bjohnson66/wayfindx/docs/Doxygen/latex/utilities_8h.tex

\doxysection{G\+:/\+Project\+\_\+\+Files/\+Way\+Find\+X/wfx\+\_\+sw/wfx\+\_\+sw/ut/utilities.h File Reference}
\hypertarget{utilities_8h}{}\label{utilities_8h}\index{G:/Project\_Files/WayFindX/wfx\_sw/wfx\_sw/ut/utilities.h@{G:/Project\_Files/WayFindX/wfx\_sw/wfx\_sw/ut/utilities.h}}

Header file containing common utility functions and definitions.  

{\ttfamily \#include "{}ut\+\_\+types.\+h"{}}\newline
{\ttfamily \#include "{}../nf/nf\+\_\+types.\+h"{}}\newline
\doxysubsubsection*{Macros}
\begin{DoxyCompactItemize}
\item 
\#define \mbox{\hyperlink{utilities_8h_a700f88377bf36711b711f69b06c52f5d}{NOP}}~asm("{}nop"{});
\item 
\#define \mbox{\hyperlink{utilities_8h_a3c5465ec3dcb8f48d76b9961625cfb26}{STAT\+\_\+\+MODE}}~1
\item 
\#define \mbox{\hyperlink{utilities_8h_a2c6fab7bc1954d43f20ddcf3241d374f}{NAV\+\_\+\+MODE}}~0
\item 
\#define \mbox{\hyperlink{utilities_8h_a15ce356b42b1e66c0e5287551fbcd371}{NUM\+\_\+\+OPERATIONS}}~3
\item 
\#define \mbox{\hyperlink{utilities_8h_a44262718e6ca1ed8813bac3fe8c817c8}{SAVE\+\_\+\+OP}}~0
\item 
\#define \mbox{\hyperlink{utilities_8h_a8d067386e33f9d834262ff6bef0b4e0e}{CLEAR\+\_\+\+OP}}~1
\item 
\#define \mbox{\hyperlink{utilities_8h_a6dda44ab465064ec1dd8254e31b32d3d}{RESET\+\_\+\+OP}}~2
\item 
\#define \mbox{\hyperlink{utilities_8h_a30682ad456c44dd32e1da9094a40d97f}{MAX\+\_\+\+MEM\+\_\+\+INDEX}}~10
\item 
\#define \mbox{\hyperlink{utilities_8h_ac859a452892e212dd0cdbedf6f17318d}{SAVE\+\_\+\+STR}}~"{} SAVE"{}
\item 
\#define \mbox{\hyperlink{utilities_8h_a315549aca62f71abb3dfe8fd1770039a}{CLEAR\+\_\+\+STR}}~"{}CLEAR"{}
\item 
\#define \mbox{\hyperlink{utilities_8h_a3d3c836976b73a779f04cec0548df7c8}{RESET\+\_\+\+STR}}~"{}RESET"{}
\item 
\#define \mbox{\hyperlink{utilities_8h_a45add6b39f5b0c0137de978b90e26b5d}{NUM\+\_\+\+BUTTONS}}~4
\item 
\#define \mbox{\hyperlink{utilities_8h_a665ea61ca014eadbe2547eaf1b937fc3}{MODE\+\_\+\+SELECT\+\_\+\+BTN}}~PINC0
\item 
\#define \mbox{\hyperlink{utilities_8h_ae26947bd73f06a8fbe1720b9f1d0b4b0}{MEM\+\_\+\+SELECT\+\_\+\+BTN}}~PINC1
\item 
\#define \mbox{\hyperlink{utilities_8h_a1c07d5e59549b9f820a7f914cc9268e3}{OP\+\_\+\+SELECT\+\_\+\+BTN}}~PINC2
\item 
\#define \mbox{\hyperlink{utilities_8h_a8c37fc7873fc7e7e8f6c9a02f02e3a81}{ACTION\+\_\+\+BTN}}~PINC3
\item 
\#define \mbox{\hyperlink{utilities_8h_a6e14e133a57aa56366a16aa61f11453f}{ON\+\_\+\+TIME\+\_\+\+THRESHHOLD}}~(\mbox{\hyperlink{ut__types_8h_a1f1825b69244eb3ad2c7165ddc99c956}{uint16\+\_\+t}})100
\item 
\#define \mbox{\hyperlink{utilities_8h_a76b15c613ec428b45529947b62420051}{RESET\+\_\+\+TIME\+\_\+\+THRESHHOLD}}~(\mbox{\hyperlink{ut__types_8h_a1f1825b69244eb3ad2c7165ddc99c956}{uint16\+\_\+t}})30
\end{DoxyCompactItemize}
\doxysubsubsection*{Functions}
\begin{DoxyCompactItemize}
\item 
void \mbox{\hyperlink{utilities_8h_a435a2ff90939883d4bf4aa83f03cd2b4}{ut\+\_\+init}} ()
\begin{DoxyCompactList}\small\item\em Initializes the pins for buttons, loads from SD card, and initializes stored locations on startup. \end{DoxyCompactList}\item 
void \mbox{\hyperlink{utilities_8h_a88ffabf71aed5f9ff12e47960d74ad3a}{ut\+\_\+poll\+\_\+btns}} ()
\begin{DoxyCompactList}\small\item\em Checks status of each button sequentially. Action triggers on button release. Is to be called in background via interrupt. Post-\/polling action takes place in the following order\+: MODE\+\_\+\+SELECT\+\_\+\+BTN, MEM\+\_\+\+SELECT\+\_\+\+BTN, OP\+\_\+\+SELECT\+\_\+\+BTN. \end{DoxyCompactList}\end{DoxyCompactItemize}
\doxysubsubsection*{Variables}
\begin{DoxyCompactItemize}
\item 
\mbox{\hyperlink{ut__types_8h_a5338510a6d3a27844de9a766a4303d46}{boolean\+\_\+t}} \mbox{\hyperlink{utilities_8h_af78821a90ed17b6589cce61366448631}{ut\+\_\+mode}}
\item 
\mbox{\hyperlink{ut__types_8h_aba7bc1797add20fe3efdf37ced1182c5}{uint8\+\_\+t}} \mbox{\hyperlink{utilities_8h_a59ef0619f0fca92ab12dccac00503277}{ut\+\_\+operation}}
\item 
\mbox{\hyperlink{ut__types_8h_aba7bc1797add20fe3efdf37ced1182c5}{uint8\+\_\+t}} \mbox{\hyperlink{utilities_8h_aab6073f815c4c183a282ab1f8831e75a}{ut\+\_\+memory\+\_\+0idx}}
\item 
float \mbox{\hyperlink{utilities_8h_a41b8ed1a1c1e54b0bc8bd88cd0731187}{ut\+\_\+lat\+\_\+mem\+\_\+floats}} \mbox{[}\mbox{\hyperlink{utilities_8h_a30682ad456c44dd32e1da9094a40d97f}{MAX\+\_\+\+MEM\+\_\+\+INDEX}}\mbox{]}
\item 
float \mbox{\hyperlink{utilities_8h_a07f10ac2a8fd49e014aa87de20167da3}{ut\+\_\+long\+\_\+mem\+\_\+floats}} \mbox{[}\mbox{\hyperlink{utilities_8h_a30682ad456c44dd32e1da9094a40d97f}{MAX\+\_\+\+MEM\+\_\+\+INDEX}}\mbox{]}
\item 
char \mbox{\hyperlink{utilities_8h_ab7665b726dd42a9d5c9af514c3119768}{ut\+\_\+lat\+\_\+mem\+\_\+str}} \mbox{[}\mbox{\hyperlink{nf__types_8h_a7b3c9ba3ceea8208b4b82e11a41722e8}{LLA\+\_\+\+LAT\+\_\+\+BUFFER\+\_\+\+SIZE}}\mbox{]}
\item 
char \mbox{\hyperlink{utilities_8h_a22d6ca202177fcc59702e055ebb0e1e1}{ut\+\_\+long\+\_\+mem\+\_\+str}} \mbox{[}\mbox{\hyperlink{nf__types_8h_a548e32055b21b64df9a5c859e1be38d4}{LLA\+\_\+\+LONG\+\_\+\+BUFFER\+\_\+\+SIZE}}\mbox{]}
\end{DoxyCompactItemize}

\doxysubsection{Detailed Description}
Header file containing common utility functions and definitions. 

This file provides declarations for common utility functions and definitions that can be used throughout the project. \begin{DoxyVersion}{Version}
1.\+0 
\end{DoxyVersion}
\begin{DoxyCopyright}{Copyright}
(C) 2024 Bradley Johnson and Abele Atresso 
\end{DoxyCopyright}

Definition in file \mbox{\hyperlink{utilities_8h_source}{utilities.\+h}}.

\doxysubsection{Macro Definition Documentation}
\Hypertarget{utilities_8h_a8c37fc7873fc7e7e8f6c9a02f02e3a81}\label{utilities_8h_a8c37fc7873fc7e7e8f6c9a02f02e3a81} 
\index{utilities.h@{utilities.h}!ACTION\_BTN@{ACTION\_BTN}}
\index{ACTION\_BTN@{ACTION\_BTN}!utilities.h@{utilities.h}}
\doxysubsubsection{\texorpdfstring{ACTION\_BTN}{ACTION\_BTN}}
{\footnotesize\ttfamily \#define ACTION\+\_\+\+BTN~PINC3}

Action button pin. 

Definition at line \mbox{\hyperlink{utilities_8h_source_l00036}{36}} of file \mbox{\hyperlink{utilities_8h_source}{utilities.\+h}}.

\Hypertarget{utilities_8h_a8d067386e33f9d834262ff6bef0b4e0e}\label{utilities_8h_a8d067386e33f9d834262ff6bef0b4e0e} 
\index{utilities.h@{utilities.h}!CLEAR\_OP@{CLEAR\_OP}}
\index{CLEAR\_OP@{CLEAR\_OP}!utilities.h@{utilities.h}}
\doxysubsubsection{\texorpdfstring{CLEAR\_OP}{CLEAR\_OP}}
{\footnotesize\ttfamily \#define CLEAR\+\_\+\+OP~1}

Clear operation index. 

Definition at line \mbox{\hyperlink{utilities_8h_source_l00024}{24}} of file \mbox{\hyperlink{utilities_8h_source}{utilities.\+h}}.

\Hypertarget{utilities_8h_a315549aca62f71abb3dfe8fd1770039a}\label{utilities_8h_a315549aca62f71abb3dfe8fd1770039a} 
\index{utilities.h@{utilities.h}!CLEAR\_STR@{CLEAR\_STR}}
\index{CLEAR\_STR@{CLEAR\_STR}!utilities.h@{utilities.h}}
\doxysubsubsection{\texorpdfstring{CLEAR\_STR}{CLEAR\_STR}}
{\footnotesize\ttfamily \#define CLEAR\+\_\+\+STR~"{}CLEAR"{}}

Clear operation string. 

Definition at line \mbox{\hyperlink{utilities_8h_source_l00029}{29}} of file \mbox{\hyperlink{utilities_8h_source}{utilities.\+h}}.

\Hypertarget{utilities_8h_a30682ad456c44dd32e1da9094a40d97f}\label{utilities_8h_a30682ad456c44dd32e1da9094a40d97f} 
\index{utilities.h@{utilities.h}!MAX\_MEM\_INDEX@{MAX\_MEM\_INDEX}}
\index{MAX\_MEM\_INDEX@{MAX\_MEM\_INDEX}!utilities.h@{utilities.h}}
\doxysubsubsection{\texorpdfstring{MAX\_MEM\_INDEX}{MAX\_MEM\_INDEX}}
{\footnotesize\ttfamily \#define MAX\+\_\+\+MEM\+\_\+\+INDEX~10}

Maximum memory index. 

Definition at line \mbox{\hyperlink{utilities_8h_source_l00027}{27}} of file \mbox{\hyperlink{utilities_8h_source}{utilities.\+h}}.

\Hypertarget{utilities_8h_ae26947bd73f06a8fbe1720b9f1d0b4b0}\label{utilities_8h_ae26947bd73f06a8fbe1720b9f1d0b4b0} 
\index{utilities.h@{utilities.h}!MEM\_SELECT\_BTN@{MEM\_SELECT\_BTN}}
\index{MEM\_SELECT\_BTN@{MEM\_SELECT\_BTN}!utilities.h@{utilities.h}}
\doxysubsubsection{\texorpdfstring{MEM\_SELECT\_BTN}{MEM\_SELECT\_BTN}}
{\footnotesize\ttfamily \#define MEM\+\_\+\+SELECT\+\_\+\+BTN~PINC1}

Memory select button pin. 

Definition at line \mbox{\hyperlink{utilities_8h_source_l00034}{34}} of file \mbox{\hyperlink{utilities_8h_source}{utilities.\+h}}.

\Hypertarget{utilities_8h_a665ea61ca014eadbe2547eaf1b937fc3}\label{utilities_8h_a665ea61ca014eadbe2547eaf1b937fc3} 
\index{utilities.h@{utilities.h}!MODE\_SELECT\_BTN@{MODE\_SELECT\_BTN}}
\index{MODE\_SELECT\_BTN@{MODE\_SELECT\_BTN}!utilities.h@{utilities.h}}
\doxysubsubsection{\texorpdfstring{MODE\_SELECT\_BTN}{MODE\_SELECT\_BTN}}
{\footnotesize\ttfamily \#define MODE\+\_\+\+SELECT\+\_\+\+BTN~PINC0}

Mode select button pin. 

Definition at line \mbox{\hyperlink{utilities_8h_source_l00033}{33}} of file \mbox{\hyperlink{utilities_8h_source}{utilities.\+h}}.

\Hypertarget{utilities_8h_a2c6fab7bc1954d43f20ddcf3241d374f}\label{utilities_8h_a2c6fab7bc1954d43f20ddcf3241d374f} 
\index{utilities.h@{utilities.h}!NAV\_MODE@{NAV\_MODE}}
\index{NAV\_MODE@{NAV\_MODE}!utilities.h@{utilities.h}}
\doxysubsubsection{\texorpdfstring{NAV\_MODE}{NAV\_MODE}}
{\footnotesize\ttfamily \#define NAV\+\_\+\+MODE~0}

Mode indicating navigation. 

Definition at line \mbox{\hyperlink{utilities_8h_source_l00020}{20}} of file \mbox{\hyperlink{utilities_8h_source}{utilities.\+h}}.

\Hypertarget{utilities_8h_a700f88377bf36711b711f69b06c52f5d}\label{utilities_8h_a700f88377bf36711b711f69b06c52f5d} 
\index{utilities.h@{utilities.h}!NOP@{NOP}}
\index{NOP@{NOP}!utilities.h@{utilities.h}}
\doxysubsubsection{\texorpdfstring{NOP}{NOP}}
{\footnotesize\ttfamily \#define NOP~asm("{}nop"{});}

No operation macro. 

Definition at line \mbox{\hyperlink{utilities_8h_source_l00017}{17}} of file \mbox{\hyperlink{utilities_8h_source}{utilities.\+h}}.

\Hypertarget{utilities_8h_a45add6b39f5b0c0137de978b90e26b5d}\label{utilities_8h_a45add6b39f5b0c0137de978b90e26b5d} 
\index{utilities.h@{utilities.h}!NUM\_BUTTONS@{NUM\_BUTTONS}}
\index{NUM\_BUTTONS@{NUM\_BUTTONS}!utilities.h@{utilities.h}}
\doxysubsubsection{\texorpdfstring{NUM\_BUTTONS}{NUM\_BUTTONS}}
{\footnotesize\ttfamily \#define NUM\+\_\+\+BUTTONS~4}

Number of buttons. 

Definition at line \mbox{\hyperlink{utilities_8h_source_l00032}{32}} of file \mbox{\hyperlink{utilities_8h_source}{utilities.\+h}}.

\Hypertarget{utilities_8h_a15ce356b42b1e66c0e5287551fbcd371}\label{utilities_8h_a15ce356b42b1e66c0e5287551fbcd371} 
\index{utilities.h@{utilities.h}!NUM\_OPERATIONS@{NUM\_OPERATIONS}}
\index{NUM\_OPERATIONS@{NUM\_OPERATIONS}!utilities.h@{utilities.h}}
\doxysubsubsection{\texorpdfstring{NUM\_OPERATIONS}{NUM\_OPERATIONS}}
{\footnotesize\ttfamily \#define NUM\+\_\+\+OPERATIONS~3}

Number of available operations. 

Definition at line \mbox{\hyperlink{utilities_8h_source_l00022}{22}} of file \mbox{\hyperlink{utilities_8h_source}{utilities.\+h}}.

\Hypertarget{utilities_8h_a6e14e133a57aa56366a16aa61f11453f}\label{utilities_8h_a6e14e133a57aa56366a16aa61f11453f} 
\index{utilities.h@{utilities.h}!ON\_TIME\_THRESHHOLD@{ON\_TIME\_THRESHHOLD}}
\index{ON\_TIME\_THRESHHOLD@{ON\_TIME\_THRESHHOLD}!utilities.h@{utilities.h}}
\doxysubsubsection{\texorpdfstring{ON\_TIME\_THRESHHOLD}{ON\_TIME\_THRESHHOLD}}
{\footnotesize\ttfamily \#define ON\+\_\+\+TIME\+\_\+\+THRESHHOLD~(\mbox{\hyperlink{ut__types_8h_a1f1825b69244eb3ad2c7165ddc99c956}{uint16\+\_\+t}})100}

Button press threshold time. 

Definition at line \mbox{\hyperlink{utilities_8h_source_l00038}{38}} of file \mbox{\hyperlink{utilities_8h_source}{utilities.\+h}}.

\Hypertarget{utilities_8h_a1c07d5e59549b9f820a7f914cc9268e3}\label{utilities_8h_a1c07d5e59549b9f820a7f914cc9268e3} 
\index{utilities.h@{utilities.h}!OP\_SELECT\_BTN@{OP\_SELECT\_BTN}}
\index{OP\_SELECT\_BTN@{OP\_SELECT\_BTN}!utilities.h@{utilities.h}}
\doxysubsubsection{\texorpdfstring{OP\_SELECT\_BTN}{OP\_SELECT\_BTN}}
{\footnotesize\ttfamily \#define OP\+\_\+\+SELECT\+\_\+\+BTN~PINC2}

Operation select button pin. 

Definition at line \mbox{\hyperlink{utilities_8h_source_l00035}{35}} of file \mbox{\hyperlink{utilities_8h_source}{utilities.\+h}}.

\Hypertarget{utilities_8h_a6dda44ab465064ec1dd8254e31b32d3d}\label{utilities_8h_a6dda44ab465064ec1dd8254e31b32d3d} 
\index{utilities.h@{utilities.h}!RESET\_OP@{RESET\_OP}}
\index{RESET\_OP@{RESET\_OP}!utilities.h@{utilities.h}}
\doxysubsubsection{\texorpdfstring{RESET\_OP}{RESET\_OP}}
{\footnotesize\ttfamily \#define RESET\+\_\+\+OP~2}

Reset operation index. 

Definition at line \mbox{\hyperlink{utilities_8h_source_l00025}{25}} of file \mbox{\hyperlink{utilities_8h_source}{utilities.\+h}}.

\Hypertarget{utilities_8h_a3d3c836976b73a779f04cec0548df7c8}\label{utilities_8h_a3d3c836976b73a779f04cec0548df7c8} 
\index{utilities.h@{utilities.h}!RESET\_STR@{RESET\_STR}}
\index{RESET\_STR@{RESET\_STR}!utilities.h@{utilities.h}}
\doxysubsubsection{\texorpdfstring{RESET\_STR}{RESET\_STR}}
{\footnotesize\ttfamily \#define RESET\+\_\+\+STR~"{}RESET"{}}

Reset operation string. 

Definition at line \mbox{\hyperlink{utilities_8h_source_l00030}{30}} of file \mbox{\hyperlink{utilities_8h_source}{utilities.\+h}}.

\Hypertarget{utilities_8h_a76b15c613ec428b45529947b62420051}\label{utilities_8h_a76b15c613ec428b45529947b62420051} 
\index{utilities.h@{utilities.h}!RESET\_TIME\_THRESHHOLD@{RESET\_TIME\_THRESHHOLD}}
\index{RESET\_TIME\_THRESHHOLD@{RESET\_TIME\_THRESHHOLD}!utilities.h@{utilities.h}}
\doxysubsubsection{\texorpdfstring{RESET\_TIME\_THRESHHOLD}{RESET\_TIME\_THRESHHOLD}}
{\footnotesize\ttfamily \#define RESET\+\_\+\+TIME\+\_\+\+THRESHHOLD~(\mbox{\hyperlink{ut__types_8h_a1f1825b69244eb3ad2c7165ddc99c956}{uint16\+\_\+t}})30}

Button release threshold time. 

Definition at line \mbox{\hyperlink{utilities_8h_source_l00039}{39}} of file \mbox{\hyperlink{utilities_8h_source}{utilities.\+h}}.

\Hypertarget{utilities_8h_a44262718e6ca1ed8813bac3fe8c817c8}\label{utilities_8h_a44262718e6ca1ed8813bac3fe8c817c8} 
\index{utilities.h@{utilities.h}!SAVE\_OP@{SAVE\_OP}}
\index{SAVE\_OP@{SAVE\_OP}!utilities.h@{utilities.h}}
\doxysubsubsection{\texorpdfstring{SAVE\_OP}{SAVE\_OP}}
{\footnotesize\ttfamily \#define SAVE\+\_\+\+OP~0}

Save operation index. 

Definition at line \mbox{\hyperlink{utilities_8h_source_l00023}{23}} of file \mbox{\hyperlink{utilities_8h_source}{utilities.\+h}}.

\Hypertarget{utilities_8h_ac859a452892e212dd0cdbedf6f17318d}\label{utilities_8h_ac859a452892e212dd0cdbedf6f17318d} 
\index{utilities.h@{utilities.h}!SAVE\_STR@{SAVE\_STR}}
\index{SAVE\_STR@{SAVE\_STR}!utilities.h@{utilities.h}}
\doxysubsubsection{\texorpdfstring{SAVE\_STR}{SAVE\_STR}}
{\footnotesize\ttfamily \#define SAVE\+\_\+\+STR~"{} SAVE"{}}

Save operation string. 

Definition at line \mbox{\hyperlink{utilities_8h_source_l00028}{28}} of file \mbox{\hyperlink{utilities_8h_source}{utilities.\+h}}.

\Hypertarget{utilities_8h_a3c5465ec3dcb8f48d76b9961625cfb26}\label{utilities_8h_a3c5465ec3dcb8f48d76b9961625cfb26} 
\index{utilities.h@{utilities.h}!STAT\_MODE@{STAT\_MODE}}
\index{STAT\_MODE@{STAT\_MODE}!utilities.h@{utilities.h}}
\doxysubsubsection{\texorpdfstring{STAT\_MODE}{STAT\_MODE}}
{\footnotesize\ttfamily \#define STAT\+\_\+\+MODE~1}

Mode indicating status. 

Definition at line \mbox{\hyperlink{utilities_8h_source_l00019}{19}} of file \mbox{\hyperlink{utilities_8h_source}{utilities.\+h}}.

\doxysubsection{Function Documentation}
\Hypertarget{utilities_8h_a435a2ff90939883d4bf4aa83f03cd2b4}\label{utilities_8h_a435a2ff90939883d4bf4aa83f03cd2b4} 
\index{utilities.h@{utilities.h}!ut\_init@{ut\_init}}
\index{ut\_init@{ut\_init}!utilities.h@{utilities.h}}
\doxysubsubsection{\texorpdfstring{ut\_init()}{ut\_init()}}
{\footnotesize\ttfamily void ut\+\_\+init (\begin{DoxyParamCaption}{ }\end{DoxyParamCaption})}

Initializes the pins for buttons, loads from SD card, and initializes stored locations on startup. 

This function initializes the pins for buttons, loads data from an SD card, and initializes stored locations on startup. 

Definition at line \mbox{\hyperlink{utilities_8c_source_l00142}{142}} of file \mbox{\hyperlink{utilities_8c_source}{utilities.\+c}}.

\Hypertarget{utilities_8h_a88ffabf71aed5f9ff12e47960d74ad3a}\label{utilities_8h_a88ffabf71aed5f9ff12e47960d74ad3a} 
\index{utilities.h@{utilities.h}!ut\_poll\_btns@{ut\_poll\_btns}}
\index{ut\_poll\_btns@{ut\_poll\_btns}!utilities.h@{utilities.h}}
\doxysubsubsection{\texorpdfstring{ut\_poll\_btns()}{ut\_poll\_btns()}}
{\footnotesize\ttfamily void ut\+\_\+poll\+\_\+btns (\begin{DoxyParamCaption}{ }\end{DoxyParamCaption})}

Checks status of each button sequentially. Action triggers on button release. Is to be called in background via interrupt. Post-\/polling action takes place in the following order\+: MODE\+\_\+\+SELECT\+\_\+\+BTN, MEM\+\_\+\+SELECT\+\_\+\+BTN, OP\+\_\+\+SELECT\+\_\+\+BTN. 

Checks status of each button sequentially. Action triggers on button release. Is to be called in background via interrupt. Post-\/polling action takes place in the following order\+: MODE\+\_\+\+SELECT\+\_\+\+BTN, MEM\+\_\+\+SELECT\+\_\+\+BTN, OP\+\_\+\+SELECT\+\_\+\+BTN.

This function checks the status of each button sequentially. Action triggers on button release. It is to be called in the background via interrupt. Post-\/polling action takes place in the following order\+: MODE\+\_\+\+SELECT\+\_\+\+BTN, MEM\+\_\+\+SELECT\+\_\+\+BTN, OP\+\_\+\+SELECT\+\_\+\+BTN. 

Definition at line \mbox{\hyperlink{utilities_8c_source_l00189}{189}} of file \mbox{\hyperlink{utilities_8c_source}{utilities.\+c}}.

\doxysubsection{Variable Documentation}
\Hypertarget{utilities_8h_a41b8ed1a1c1e54b0bc8bd88cd0731187}\label{utilities_8h_a41b8ed1a1c1e54b0bc8bd88cd0731187} 
\index{utilities.h@{utilities.h}!ut\_lat\_mem\_floats@{ut\_lat\_mem\_floats}}
\index{ut\_lat\_mem\_floats@{ut\_lat\_mem\_floats}!utilities.h@{utilities.h}}
\doxysubsubsection{\texorpdfstring{ut\_lat\_mem\_floats}{ut\_lat\_mem\_floats}}
{\footnotesize\ttfamily float ut\+\_\+lat\+\_\+mem\+\_\+floats\mbox{[}\mbox{\hyperlink{utilities_8h_a30682ad456c44dd32e1da9094a40d97f}{MAX\+\_\+\+MEM\+\_\+\+INDEX}}\mbox{]}\hspace{0.3cm}{\ttfamily [extern]}}

Array to store latitude memory floats.

Array to store latitude 

Definition at line \mbox{\hyperlink{utilities_8c_source_l00008}{8}} of file \mbox{\hyperlink{utilities_8c_source}{utilities.\+c}}.

\Hypertarget{utilities_8h_ab7665b726dd42a9d5c9af514c3119768}\label{utilities_8h_ab7665b726dd42a9d5c9af514c3119768} 
\index{utilities.h@{utilities.h}!ut\_lat\_mem\_str@{ut\_lat\_mem\_str}}
\index{ut\_lat\_mem\_str@{ut\_lat\_mem\_str}!utilities.h@{utilities.h}}
\doxysubsubsection{\texorpdfstring{ut\_lat\_mem\_str}{ut\_lat\_mem\_str}}
{\footnotesize\ttfamily char ut\+\_\+lat\+\_\+mem\+\_\+str\mbox{[}\mbox{\hyperlink{nf__types_8h_a7b3c9ba3ceea8208b4b82e11a41722e8}{LLA\+\_\+\+LAT\+\_\+\+BUFFER\+\_\+\+SIZE}}\mbox{]}\hspace{0.3cm}{\ttfamily [extern]}}

Array to store latitude memory strings.

String to store latitude 

Definition at line \mbox{\hyperlink{utilities_8c_source_l00010}{10}} of file \mbox{\hyperlink{utilities_8c_source}{utilities.\+c}}.

\Hypertarget{utilities_8h_a07f10ac2a8fd49e014aa87de20167da3}\label{utilities_8h_a07f10ac2a8fd49e014aa87de20167da3} 
\index{utilities.h@{utilities.h}!ut\_long\_mem\_floats@{ut\_long\_mem\_floats}}
\index{ut\_long\_mem\_floats@{ut\_long\_mem\_floats}!utilities.h@{utilities.h}}
\doxysubsubsection{\texorpdfstring{ut\_long\_mem\_floats}{ut\_long\_mem\_floats}}
{\footnotesize\ttfamily float ut\+\_\+long\+\_\+mem\+\_\+floats\mbox{[}\mbox{\hyperlink{utilities_8h_a30682ad456c44dd32e1da9094a40d97f}{MAX\+\_\+\+MEM\+\_\+\+INDEX}}\mbox{]}\hspace{0.3cm}{\ttfamily [extern]}}

Array to store longitude memory floats.

Array to store longitude 

Definition at line \mbox{\hyperlink{utilities_8c_source_l00009}{9}} of file \mbox{\hyperlink{utilities_8c_source}{utilities.\+c}}.

\Hypertarget{utilities_8h_a22d6ca202177fcc59702e055ebb0e1e1}\label{utilities_8h_a22d6ca202177fcc59702e055ebb0e1e1} 
\index{utilities.h@{utilities.h}!ut\_long\_mem\_str@{ut\_long\_mem\_str}}
\index{ut\_long\_mem\_str@{ut\_long\_mem\_str}!utilities.h@{utilities.h}}
\doxysubsubsection{\texorpdfstring{ut\_long\_mem\_str}{ut\_long\_mem\_str}}
{\footnotesize\ttfamily char ut\+\_\+long\+\_\+mem\+\_\+str\mbox{[}\mbox{\hyperlink{nf__types_8h_a548e32055b21b64df9a5c859e1be38d4}{LLA\+\_\+\+LONG\+\_\+\+BUFFER\+\_\+\+SIZE}}\mbox{]}\hspace{0.3cm}{\ttfamily [extern]}}

Array to store longitude memory strings.

String to store longitude 

Definition at line \mbox{\hyperlink{utilities_8c_source_l00011}{11}} of file \mbox{\hyperlink{utilities_8c_source}{utilities.\+c}}.

\Hypertarget{utilities_8h_aab6073f815c4c183a282ab1f8831e75a}\label{utilities_8h_aab6073f815c4c183a282ab1f8831e75a} 
\index{utilities.h@{utilities.h}!ut\_memory\_0idx@{ut\_memory\_0idx}}
\index{ut\_memory\_0idx@{ut\_memory\_0idx}!utilities.h@{utilities.h}}
\doxysubsubsection{\texorpdfstring{ut\_memory\_0idx}{ut\_memory\_0idx}}
{\footnotesize\ttfamily \mbox{\hyperlink{ut__types_8h_aba7bc1797add20fe3efdf37ced1182c5}{uint8\+\_\+t}} ut\+\_\+memory\+\_\+0idx\hspace{0.3cm}{\ttfamily [extern]}}

Current memory index.

Index for memory 

Definition at line \mbox{\hyperlink{utilities_8c_source_l00007}{7}} of file \mbox{\hyperlink{utilities_8c_source}{utilities.\+c}}.

\Hypertarget{utilities_8h_af78821a90ed17b6589cce61366448631}\label{utilities_8h_af78821a90ed17b6589cce61366448631} 
\index{utilities.h@{utilities.h}!ut\_mode@{ut\_mode}}
\index{ut\_mode@{ut\_mode}!utilities.h@{utilities.h}}
\doxysubsubsection{\texorpdfstring{ut\_mode}{ut\_mode}}
{\footnotesize\ttfamily \mbox{\hyperlink{ut__types_8h_a5338510a6d3a27844de9a766a4303d46}{boolean\+\_\+t}} ut\+\_\+mode\hspace{0.3cm}{\ttfamily [extern]}}

Current mode indicator.

Current mode 

Definition at line \mbox{\hyperlink{utilities_8c_source_l00005}{5}} of file \mbox{\hyperlink{utilities_8c_source}{utilities.\+c}}.

\Hypertarget{utilities_8h_a59ef0619f0fca92ab12dccac00503277}\label{utilities_8h_a59ef0619f0fca92ab12dccac00503277} 
\index{utilities.h@{utilities.h}!ut\_operation@{ut\_operation}}
\index{ut\_operation@{ut\_operation}!utilities.h@{utilities.h}}
\doxysubsubsection{\texorpdfstring{ut\_operation}{ut\_operation}}
{\footnotesize\ttfamily \mbox{\hyperlink{ut__types_8h_aba7bc1797add20fe3efdf37ced1182c5}{uint8\+\_\+t}} ut\+\_\+operation\hspace{0.3cm}{\ttfamily [extern]}}

Current operation index.

Current operation 

Definition at line \mbox{\hyperlink{utilities_8c_source_l00006}{6}} of file \mbox{\hyperlink{utilities_8c_source}{utilities.\+c}}.
